makeo/PicoLoader/flex/SolderFlex/Kicad/SolderFlex.png

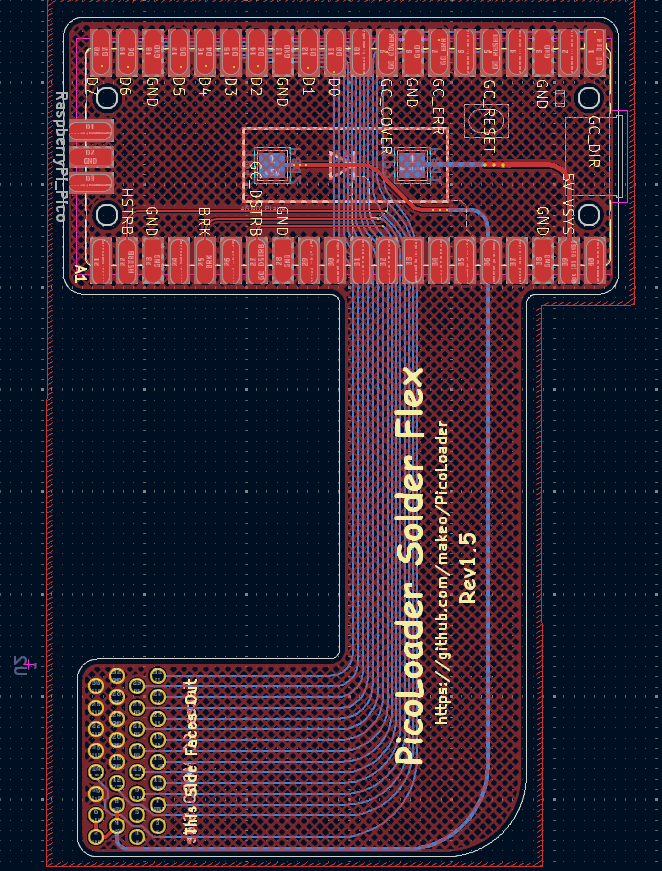
flex/SolderFlex/Kicad/SolderFlex.png
