makeo/PicoLoader/picoloader/dvd_drv.h

#ifndef DVD_DRV_H
#define DVD_DRV_H

#include <stdint.h>
#include <stdbool.h>


void dvd_drv_init();

void dvd_drv_send(const void* data, uint32_t len);
void dvd_drv_set_error();

void dvd_drv_set_cover(bool open);

bool dvd_drv_enable_passthrough();

#endif // DVD_DRV_H
